urish/real-trex-runner/3d-parts/bearing-shaft-spacer.scad

// Real Lonely T-Rex Game: Bearing Shaft Spacer
// Copyright (C) 2017, Uri Shaked and Ariella Eliassaf

$fn = 120;

difference() {
    cylinder(h=7, r=3.5);
    cylinder(h=7, r=2.5);
}    
