urish/real-trex-runner/firmware/src/game_assets.py

"""
Real Life Lonely T-Rex Game Firmware

Copyright (C) 2017-2024, Uri Shaked
"""

from asset import Asset

assets = {
    "0": Asset.load("assets/0.txt"),
    "1": Asset.load("assets/1.txt"),
    "2": Asset.load("assets/2.txt"),
    "3": Asset.load("assets/3.txt"),
    "4": Asset.load("assets/4.txt"),
    "5": Asset.load("assets/5.txt"),
    "6": Asset.load("assets/6.txt"),
    "7": Asset.load("assets/7.txt"),
    "8": Asset.load("assets/8.txt"),
    "9": Asset.load("assets/9.txt"),
    "A": Asset.load("assets/A.txt"),
    ":": Asset.load("assets/colon.txt"),
    "E": Asset.load("assets/E.txt"),
    "G": Asset.load("assets/G.txt"),
    "H": Asset.load("assets/H.txt"),
    "I": Asset.load("assets/I.txt"),
    "M": Asset.load("assets/M.txt"),
    "O": Asset.load("assets/O.txt"),
    "R": Asset.load("assets/R.txt"),
    "trex": Asset.load("assets/trex.txt"),
    "V": Asset.load("assets/V.txt"),
    "s0": Asset.load("assets/small/0.txt"),
    "s1": Asset.load("assets/small/1.txt"),
    "s2": Asset.load("assets/small/2.txt"),
    "s3": Asset.load("assets/small/3.txt"),
    "s4": Asset.load("assets/small/4.txt"),
    "s5": Asset.load("assets/small/5.txt"),
    "s6": Asset.load("assets/small/6.txt"),
    "s7": Asset.load("assets/small/7.txt"),
    "s8": Asset.load("assets/small/8.txt"),
    "s9": Asset.load("assets/small/9.txt"),
}
